tudor1610/Outer_Watch/Images/exploded_view1.png

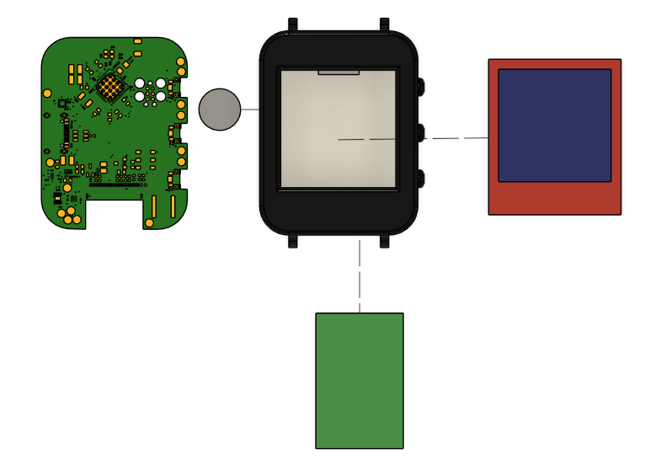
Images/exploded_view1.png
