tudor1610/Outer_Watch/Images/exploded_view3.png

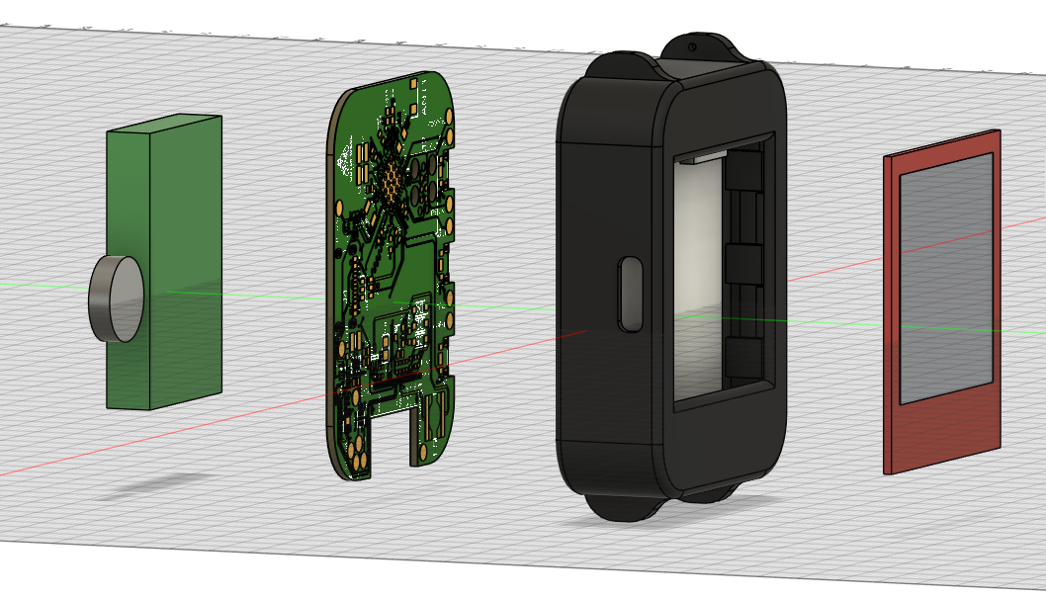
Images/exploded_view3.png
