tudor1610/Outer_Watch/Images/pbd_sketch.png

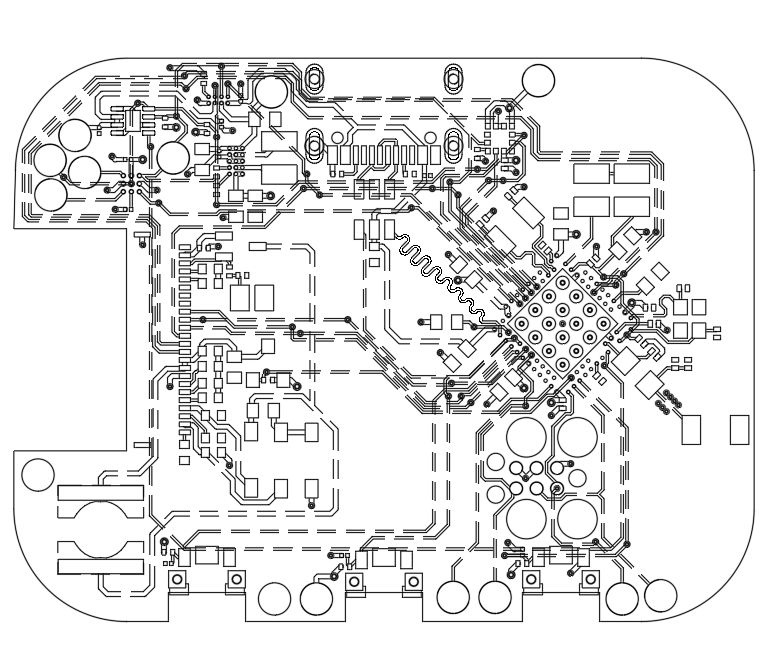
Images/pbd_sketch.png
