tudor1610/Outer_Watch/Images/pcb_back.png

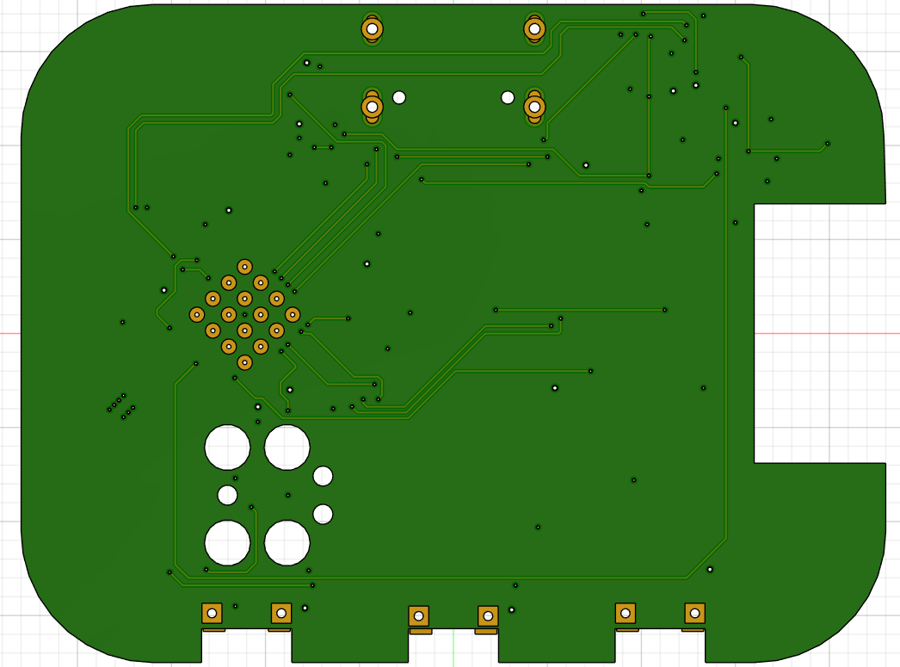
Images/pcb_back.png
