tudor1610/Outer_Watch/Images/assembly_side.png

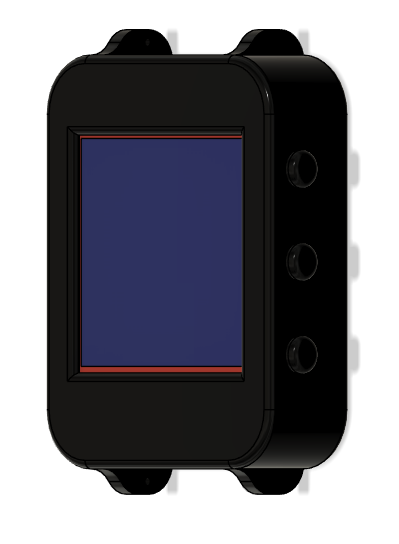
Images/assembly_side.png
