tudor1610/Outer_Watch/Images/assembly_top.png

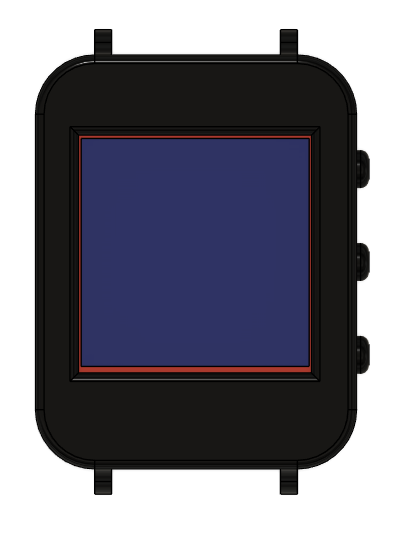
Images/assembly_top.png
